MrBeeboh/JeNo7-Sentinel-RTK/JeNo-7-main/04-TPU-HISTORY/JeNo7_1.0.0_Session_High_Tilt.stl

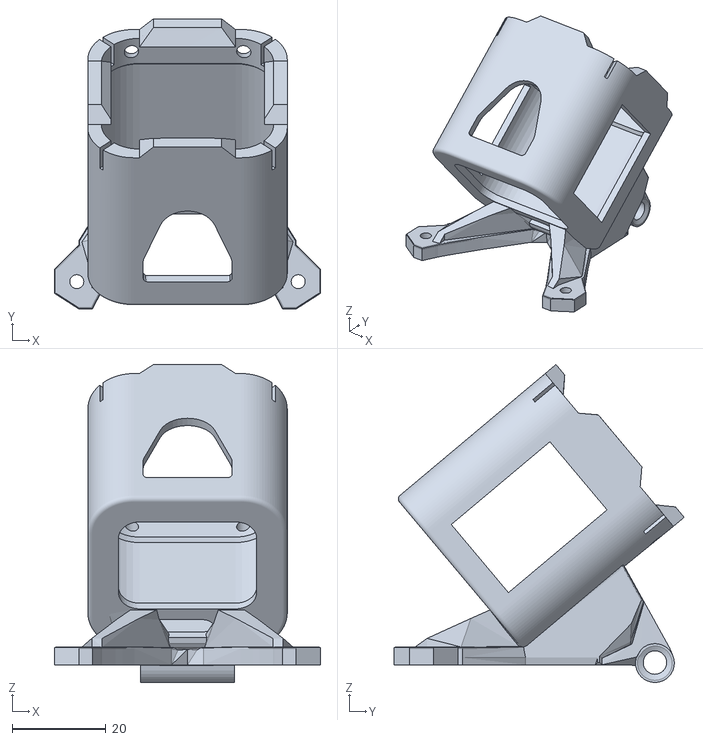
[picture p15: CAD file, 2026-07-24]
JeNo-7-main/04-TPU-HISTORY/JeNo7_1.0.0_Session_High_Tilt.stl
56.9 x 62.0 x 67.9
