MrBeeboh/JeNo7-Sentinel-RTK/Sentinel-on-JeNo7/LR900_Mount.stl

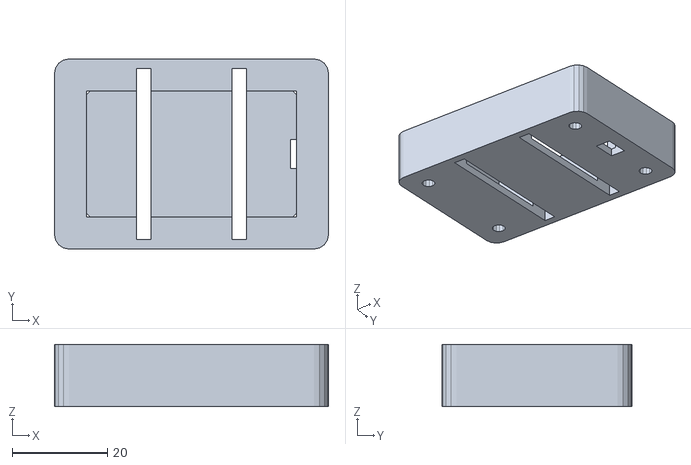
[picture p16: CAD file, 2026-07-24]
Sentinel-on-JeNo7/LR900_Mount.stl
57.4 x 39.8 x 13.0
