MrBeeboh/JeNo7-Sentinel-RTK/Editable/01-CARBON-3D/Arm_key_EditReady.FCStd

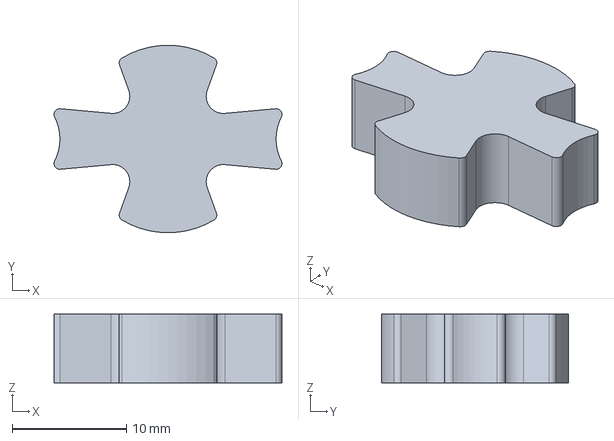
[picture p17: CAD file, 2026-07-24]
Editable/01-CARBON-3D/Arm_key_EditReady.FCStd
20.0 x 16.4 x 6.00 mm
