MrBeeboh/JeNo7-Sentinel-RTK/Editable/02-CARBON-2D-DXF/from-step-projection/Middle_plate_2p5mm.dxf

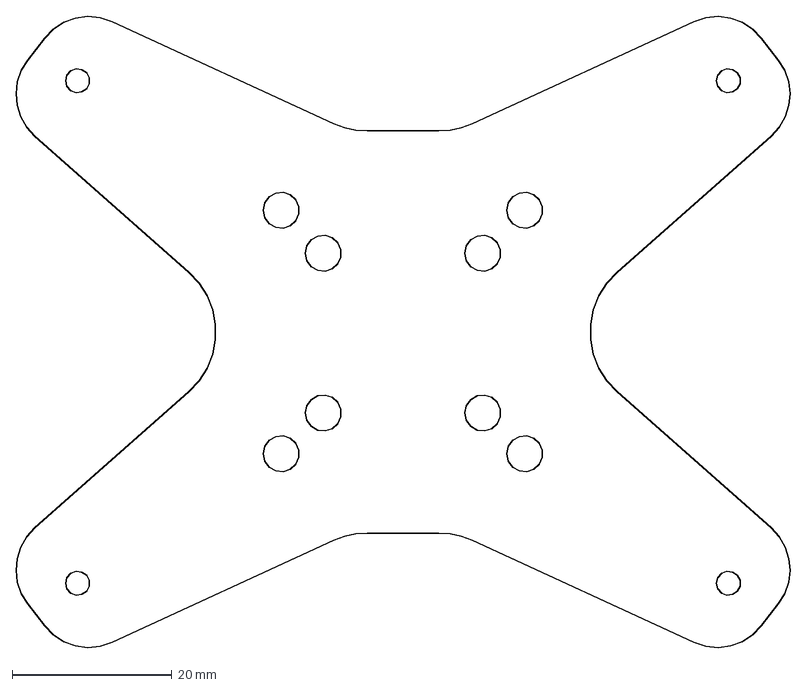
[picture p19: CAD file, 2026-07-24]
Editable/02-CARBON-2D-DXF/from-step-projection/Middle_plate_2p5mm.dxf
96.9 x 79.0 mm
