MrBeeboh/JeNo7-Sentinel-RTK/Editable/03-TPU-3D/from-assembly-STEP/TPU_Rear_bumper.step

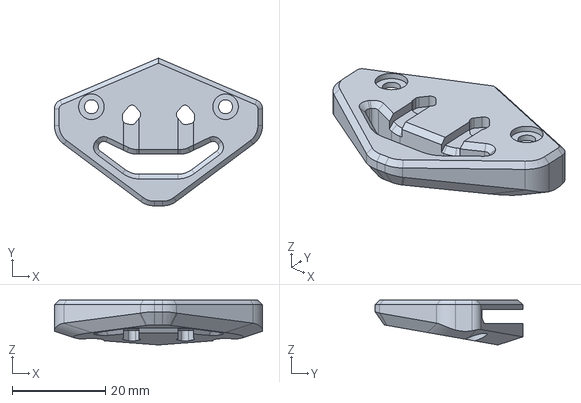
[picture p20: CAD file, 2026-07-24]
Editable/03-TPU-3D/from-assembly-STEP/TPU_Rear_bumper.step
44.7 x 31.8 x 9.65 mm
