MrBeeboh/JeNo7-Sentinel-RTK/JeNo-7-main/02-TPU/JeNo7_Antenna_Double_SMA.stl

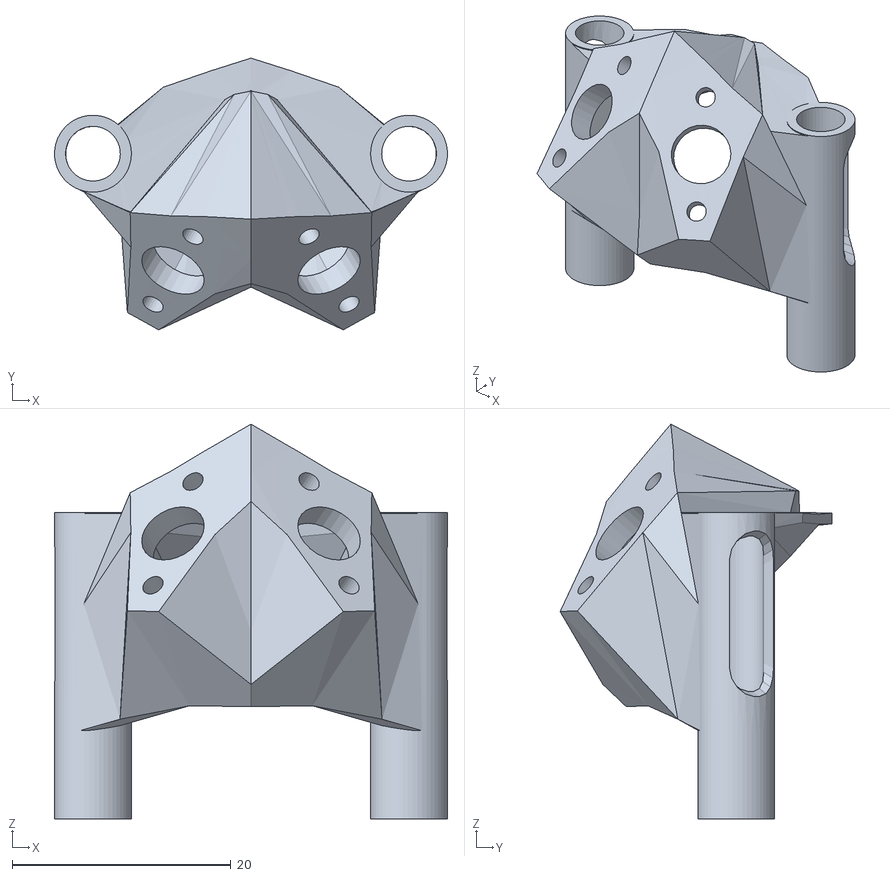
[picture p21: CAD file, 2026-07-24]
JeNo-7-main/02-TPU/JeNo7_Antenna_Double_SMA.stl
35.9 x 24.8 x 36.1
