MrBeeboh/JeNo7-Sentinel-RTK/JeNo-7-main/04-TPU-HISTORY/JeNo7_1.0.0_Soft_Mount_Cine_Plate.stl

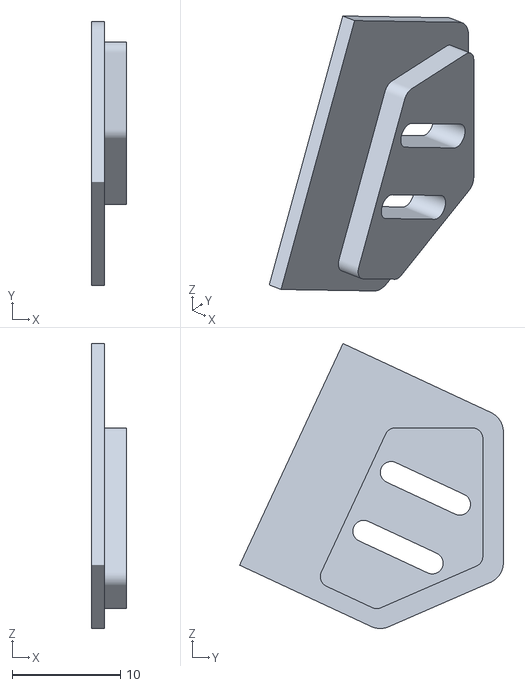
[picture p22: CAD file, 2026-07-24]
JeNo-7-main/04-TPU-HISTORY/JeNo7_1.0.0_Soft_Mount_Cine_Plate.stl
3.20 x 24.4 x 26.4
