MrBeeboh/JeNo7-Sentinel-RTK/Sentinel-on-JeNo7/RP3_Mount.stl

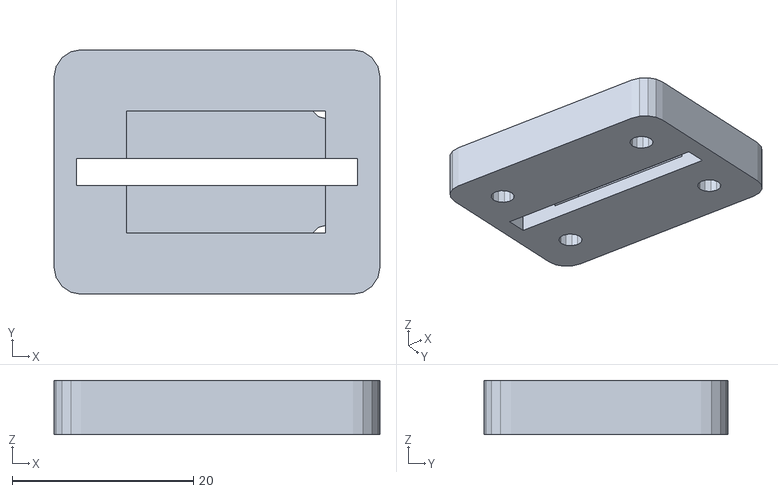
[picture p23: CAD file, 2026-07-24]
Sentinel-on-JeNo7/RP3_Mount.stl
36.0 x 27.0 x 6.00
