MrBeeboh/JeNo7-Sentinel-RTK/Editable/01-CARBON-3D/Camera_plate_25deg_O4.step

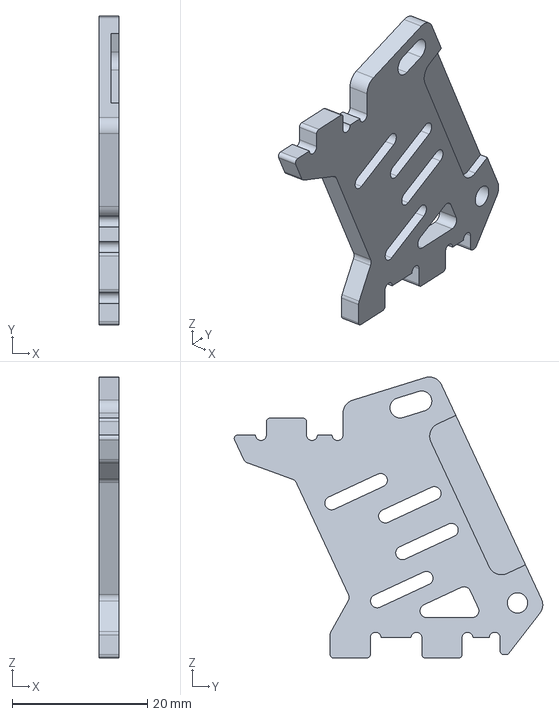
[picture p24: CAD file, 2026-07-24]
Editable/01-CARBON-3D/Camera_plate_25deg_O4.step
3.00 x 45.7 x 41.6 mm
