MrBeeboh/JeNo7-Sentinel-RTK/Editable/02-CARBON-2D-DXF/from-step-projection/Top_plate_2p5mm.dxf

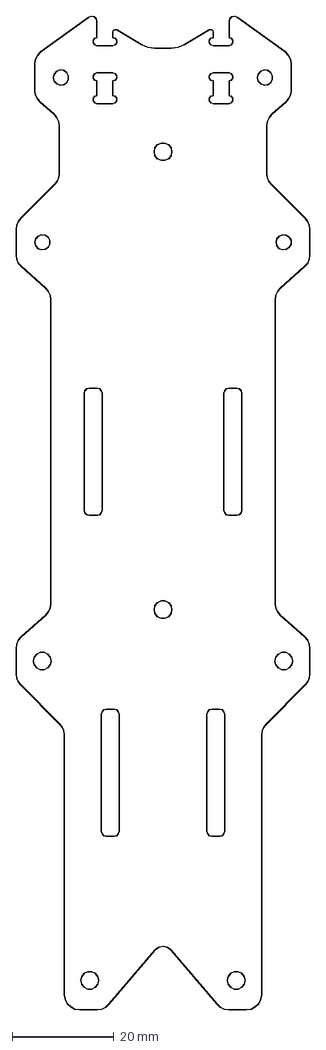
[picture p26: CAD file, 2026-07-24]
Editable/02-CARBON-2D-DXF/from-step-projection/Top_plate_2p5mm.dxf
57.8 x 195.4 mm
