MrBeeboh/JeNo7-Sentinel-RTK/Editable/03-TPU-3D/from-assembly-STEP/TPU_Antenna_support.step

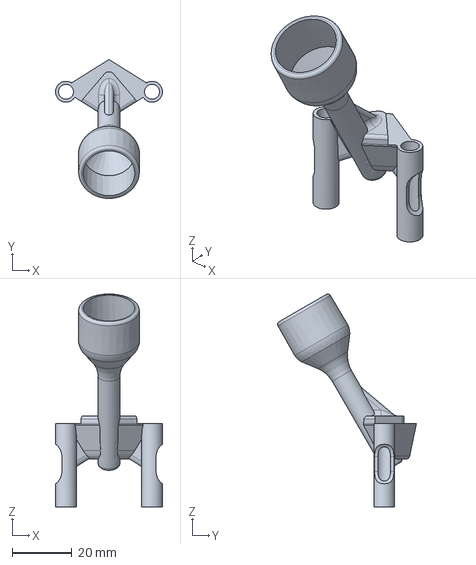
[picture p27: CAD file, 2026-07-24]
Editable/03-TPU-3D/from-assembly-STEP/TPU_Antenna_support.step
35.8 x 46.5 x 71.3 mm
