MrBeeboh/JeNo7-Sentinel-RTK/JeNo-7-main/04-TPU-HISTORY/JeNo7_1.0.0_Gopro_40deg.stl

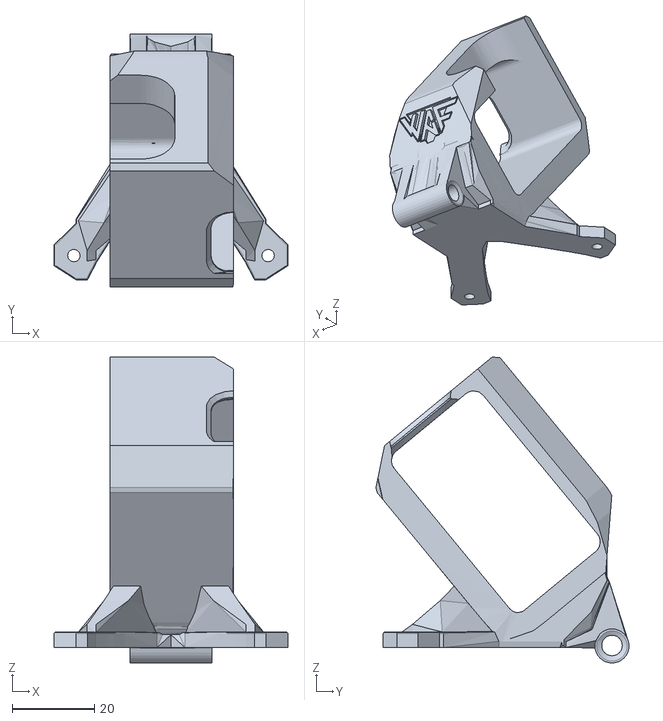
[picture p28: CAD file, 2026-07-24]
JeNo-7-main/04-TPU-HISTORY/JeNo7_1.0.0_Gopro_40deg.stl
56.9 x 61.6 x 74.5
