MrBeeboh/JeNo7-Sentinel-RTK/Sentinel-on-JeNo7/GNSS_Roof_Plate.stl

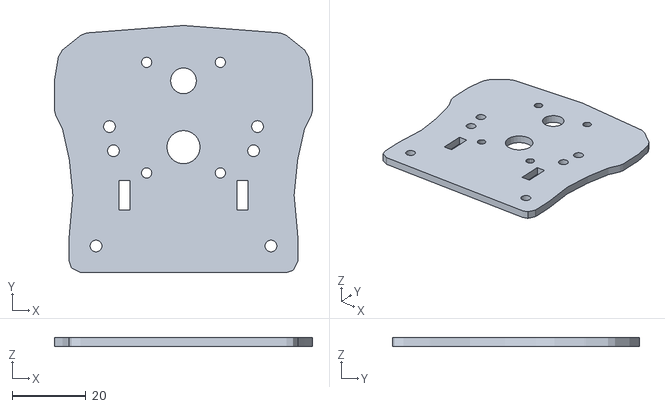
[picture p29: CAD file, 2026-07-24]
Sentinel-on-JeNo7/GNSS_Roof_Plate.stl
70.0 x 67.0 x 2.50
