MrBeeboh/JeNo7-Sentinel-RTK/Editable/01-CARBON-3D/Bottom_plate_3mm_EditReady.FCStd

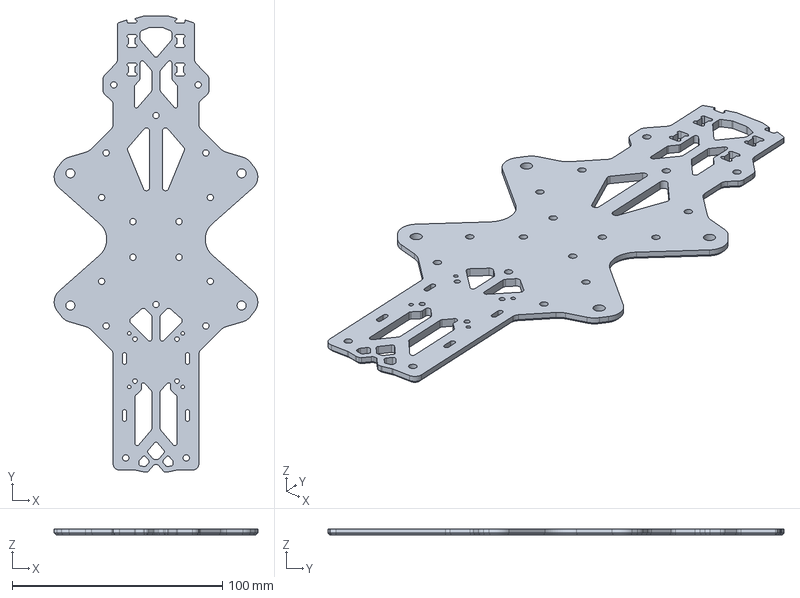
[picture p30: CAD file, 2026-07-24]
Editable/01-CARBON-3D/Bottom_plate_3mm_EditReady.FCStd
96.9 x 217.1 x 3.00 mm
