MrBeeboh/JeNo7-Sentinel-RTK/Editable/02-CARBON-2D-DXF/from-all-versions-dxf/Arm_or_reinforcement_14.dxf

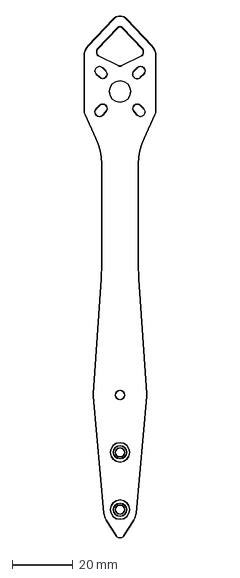
[picture p31: CAD file, 2026-07-24]
Editable/02-CARBON-2D-DXF/from-all-versions-dxf/Arm_or_reinforcement_14.dxf
23.5 x 171.2 mm
