MrBeeboh/JeNo7-Sentinel-RTK/Editable/02-CARBON-2D-DXF/from-step-projection/Arm_key.dxf

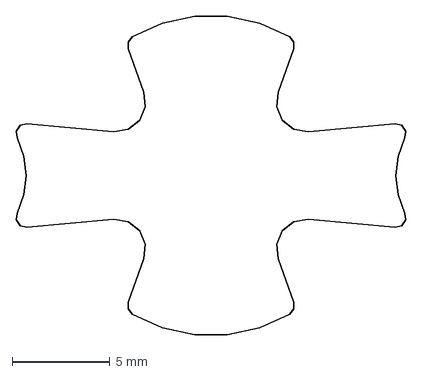
[picture p32: CAD file, 2026-07-24]
Editable/02-CARBON-2D-DXF/from-step-projection/Arm_key.dxf
19.9 x 16.3 mm
