MrBeeboh/JeNo7-Sentinel-RTK/JeNo-7-main/02-TPU/JeNo7_Antenna_Front_RX_Support.stl

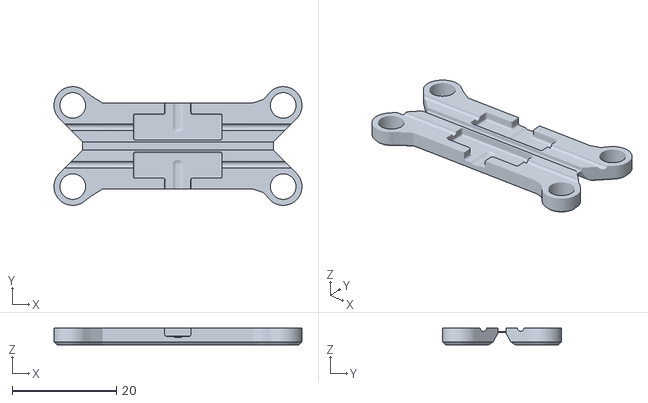
[picture p33: CAD file, 2026-07-24]
JeNo-7-main/02-TPU/JeNo7_Antenna_Front_RX_Support.stl
47.5 x 22.7 x 3.20
