MrBeeboh/JeNo7-Sentinel-RTK/JeNo-7-main/04-TPU-HISTORY/JeNo7_1.0.0_Gopro_25deg.stl

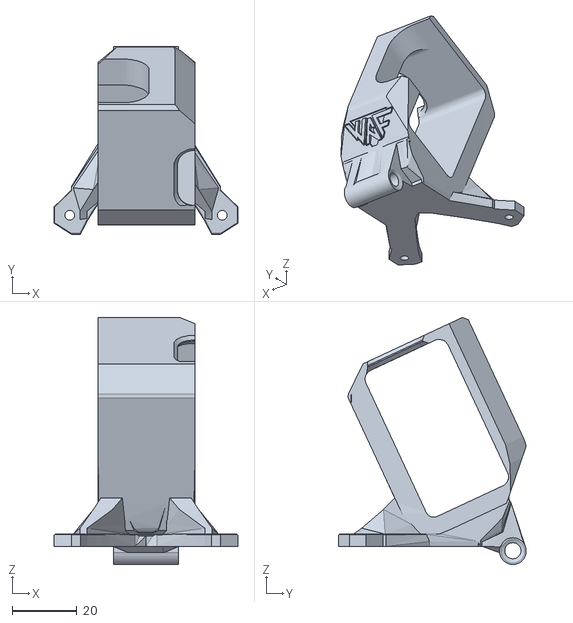
[picture p34: CAD file, 2026-07-24]
JeNo-7-main/04-TPU-HISTORY/JeNo7_1.0.0_Gopro_25deg.stl
56.9 x 58.1 x 76.5
