MrBeeboh/JeNo7-Sentinel-RTK/Sentinel-on-JeNo7/GNSS_Roof_Plate_fc.step

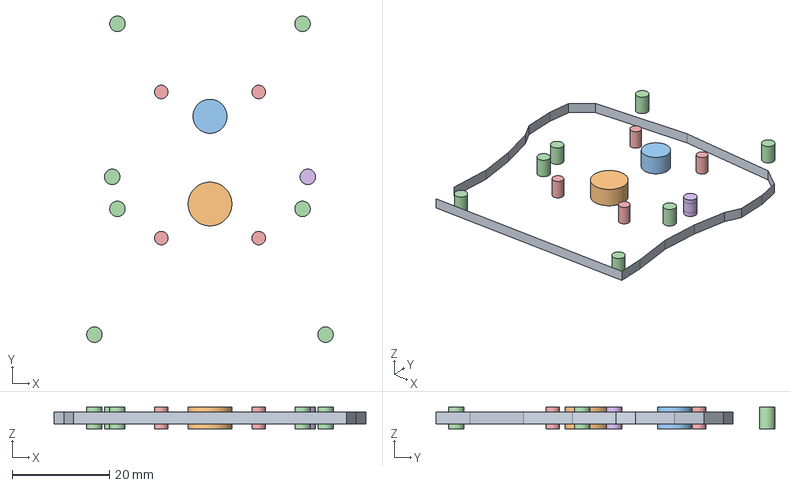
[picture p35: CAD file, 2026-07-24]
Sentinel-on-JeNo7/GNSS_Roof_Plate_fc.step
64.0 x 69.6 x 4.50 mm
