MrBeeboh/JeNo7-Sentinel-RTK/Editable/02-CARBON-2D-DXF/from-all-versions-dxf/Plate_22_20x16mm.dxf

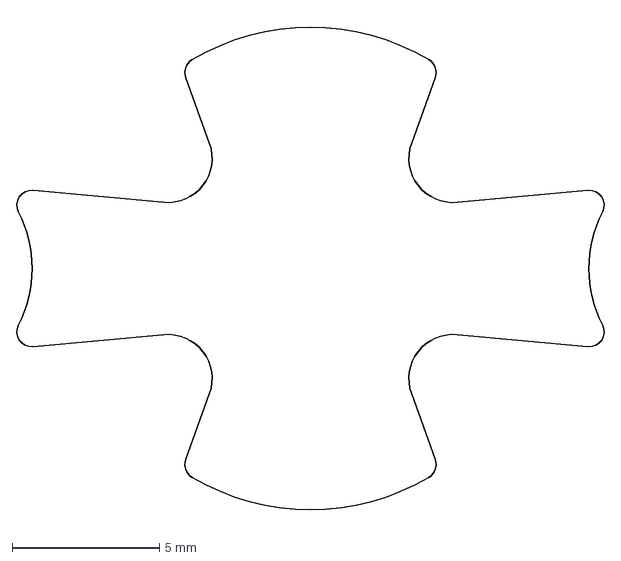
[picture p36: CAD file, 2026-07-24]
Editable/02-CARBON-2D-DXF/from-all-versions-dxf/Plate_22_20x16mm.dxf
20.0 x 17.1 mm
