MrBeeboh/JeNo7-Sentinel-RTK/Editable/02-CARBON-2D-DXF/from-step-projection/Bottom_plate_3mm.dxf

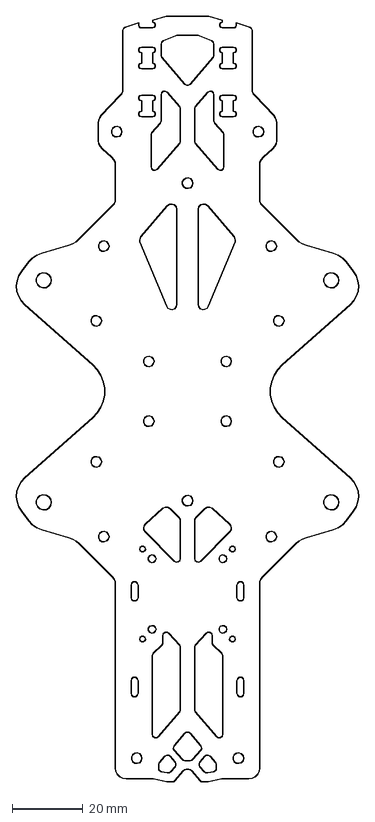
[picture p37: CAD file, 2026-07-24]
Editable/02-CARBON-2D-DXF/from-step-projection/Bottom_plate_3mm.dxf
96.9 x 217.1 mm
