MrBeeboh/JeNo7-Sentinel-RTK/JeNo-7-main/02-TPU/JeNo7_Arm_6mm.stl

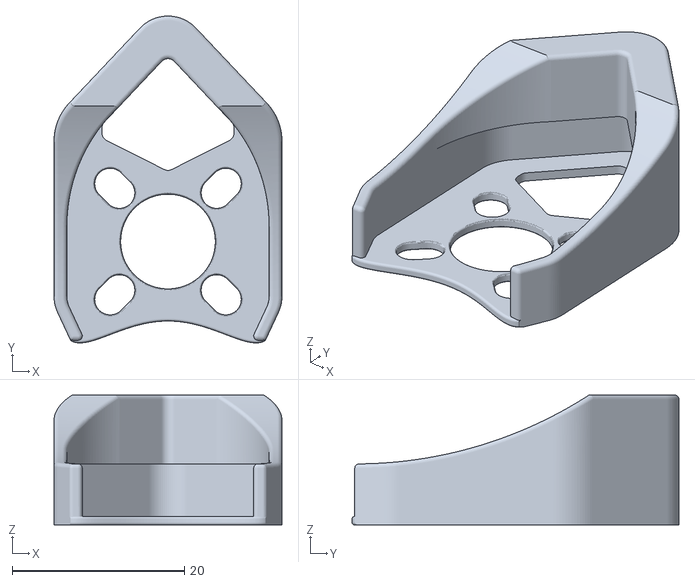
[picture p38: CAD file, 2026-07-24]
JeNo-7-main/02-TPU/JeNo7_Arm_6mm.stl
26.5 x 38.0 x 15.1
