MrBeeboh/JeNo7-Sentinel-RTK/Editable/01-CARBON-3D/Arm_8mm.step

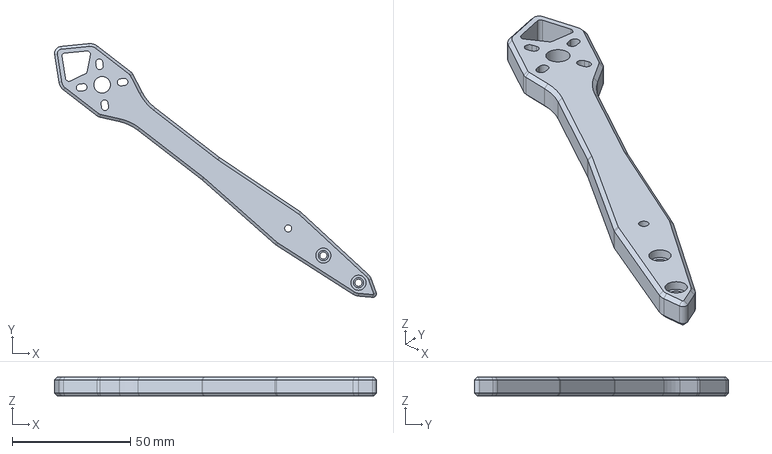
[picture p39: CAD file, 2026-07-24]
Editable/01-CARBON-3D/Arm_8mm.step
136.4 x 107.6 x 8.00 mm
