MrBeeboh/JeNo7-Sentinel-RTK/JeNo-7-main/02-TPU/JeNo7_Soft_Mount_Cine_Plate_O3_O4.stl

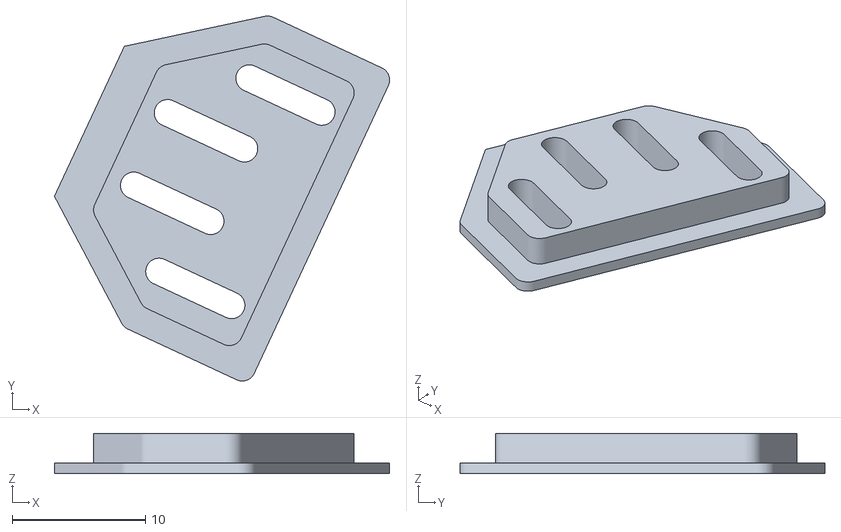
[picture p40: CAD file, 2026-07-24]
JeNo-7-main/02-TPU/JeNo7_Soft_Mount_Cine_Plate_O3_O4.stl
25.1 x 27.4 x 3.00
