MrBeeboh/JeNo7-Sentinel-RTK/Editable/02-CARBON-2D-DXF/from-all-versions-dxf/Top_plate_variant_05.dxf

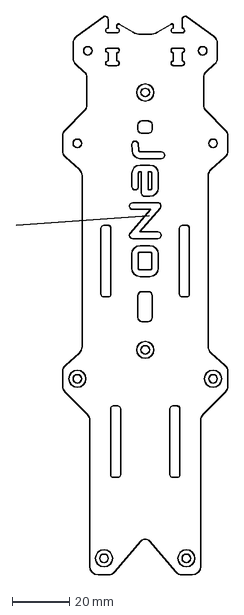
[picture p41: CAD file, 2026-07-24]
Editable/02-CARBON-2D-DXF/from-all-versions-dxf/Top_plate_variant_05.dxf
74.0 x 195.5 mm
