MrBeeboh/JeNo7-Sentinel-RTK/Editable/02-CARBON-2D-DXF/from-all-versions-dxf/Camera_plate_variant_09.dxf

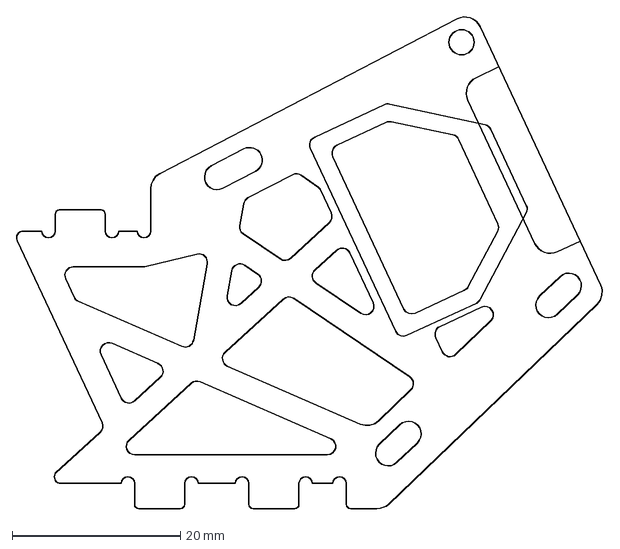
[picture p42: CAD file, 2026-07-24]
Editable/02-CARBON-2D-DXF/from-all-versions-dxf/Camera_plate_variant_09.dxf
69.8 x 58.5 mm
