MrBeeboh/JeNo7-Sentinel-RTK/JeNo-7-main/02-TPU/JeNo7_Capacitor_50V_Spike_Support.stl

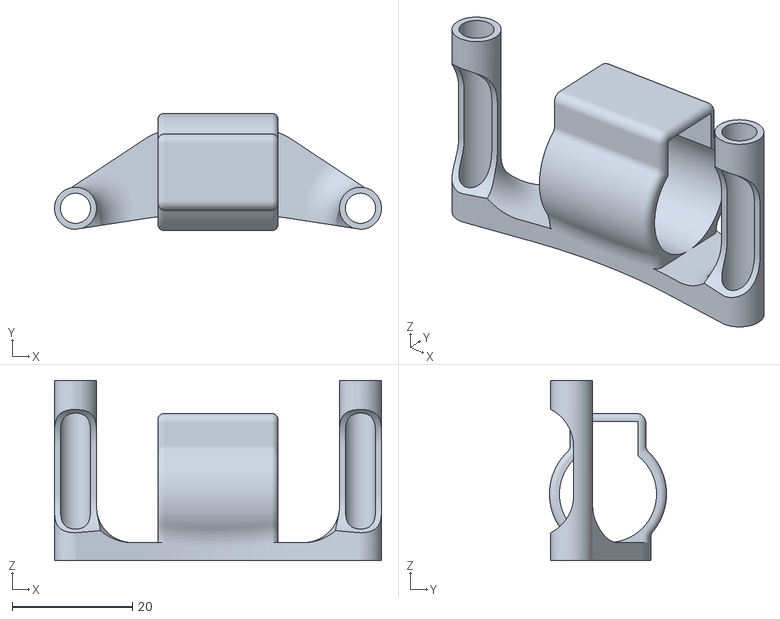
[picture p43: CAD file, 2026-07-24]
JeNo-7-main/02-TPU/JeNo7_Capacitor_50V_Spike_Support.stl
54.5 x 19.5 x 30.0
