MrBeeboh/JeNo7-Sentinel-RTK/Editable/02-CARBON-2D-DXF/from-all-versions-dxf/Plate_20_46x42mm.dxf

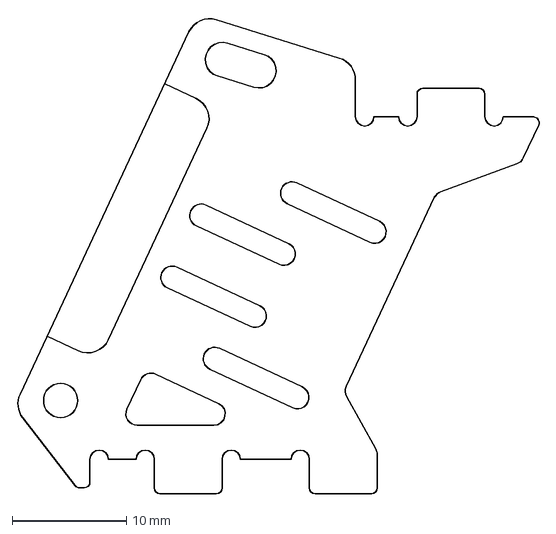
[picture p44: CAD file, 2026-07-24]
Editable/02-CARBON-2D-DXF/from-all-versions-dxf/Plate_20_46x42mm.dxf
45.8 x 41.8 mm
