MrBeeboh/JeNo7-Sentinel-RTK/Editable/02-CARBON-2D-DXF/from-all-versions-dxf/Arm_or_reinforcement_08.dxf

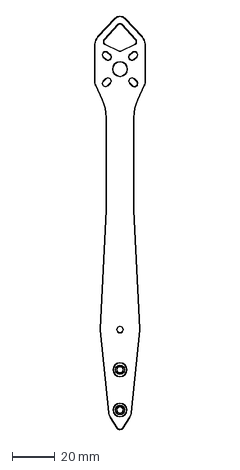
[picture p46: CAD file, 2026-07-24]
Editable/02-CARBON-2D-DXF/from-all-versions-dxf/Arm_or_reinforcement_08.dxf
23.5 x 193.7 mm
