MrBeeboh/JeNo7-Sentinel-RTK/JeNo-7-main/02-TPU/JeNo7_Antenna_SMA_T-Antenna.stl

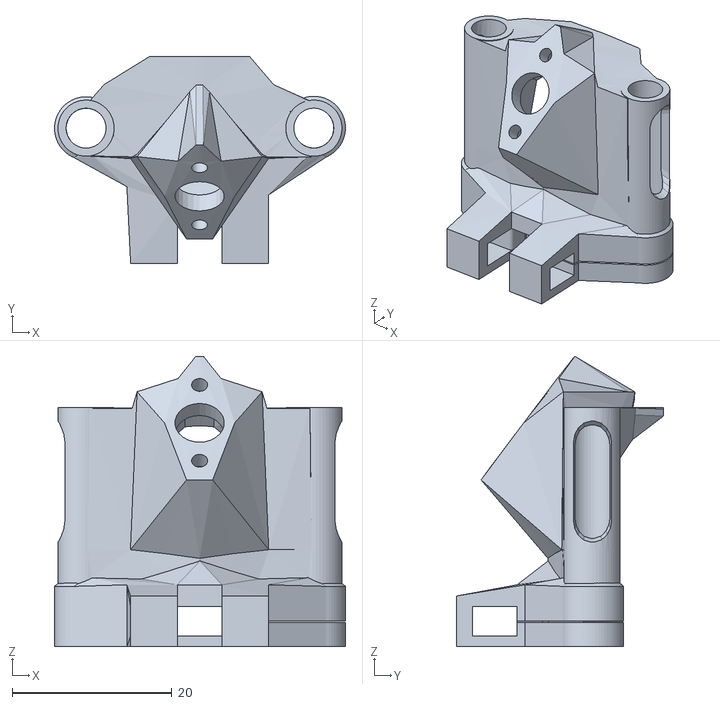
[picture p47: CAD file, 2026-07-24]
JeNo-7-main/02-TPU/JeNo7_Antenna_SMA_T-Antenna.stl
36.4 x 25.9 x 36.4
