MrBeeboh/JeNo7-Sentinel-RTK/Editable/02-CARBON-2D-DXF/from-all-versions-dxf/Middle_plate_variant_07.dxf

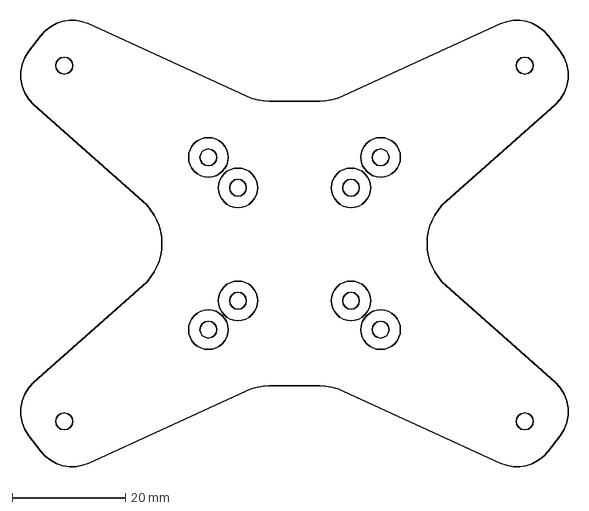
[picture p48: CAD file, 2026-07-24]
Editable/02-CARBON-2D-DXF/from-all-versions-dxf/Middle_plate_variant_07.dxf
98.5 x 80.5 mm
