MrBeeboh/JeNo7-Sentinel-RTK/Editable/02-CARBON-2D-DXF/from-all-versions-dxf/Plate_18_52x43mm.dxf

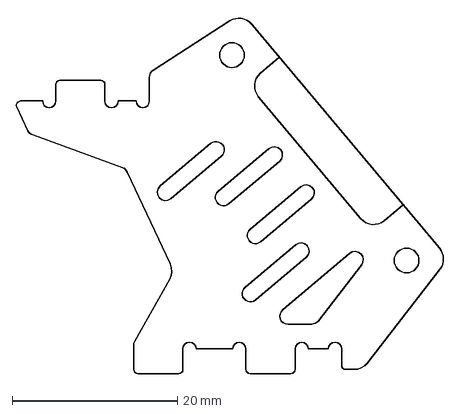
[picture p50: CAD file, 2026-07-24]
Editable/02-CARBON-2D-DXF/from-all-versions-dxf/Plate_18_52x43mm.dxf
51.9 x 43.2 mm
