MrBeeboh/JeNo7-Sentinel-RTK/Editable/02-CARBON-2D-DXF/from-all-versions-dxf/Bottom_plate_variant_02.dxf

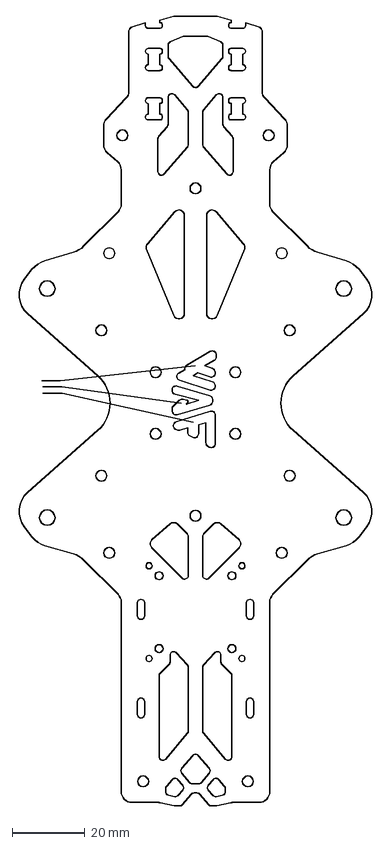
[picture p52: CAD file, 2026-07-24]
Editable/02-CARBON-2D-DXF/from-all-versions-dxf/Bottom_plate_variant_02.dxf
98.5 x 217.1 mm
