MrBeeboh/JeNo7-Sentinel-RTK/Editable/02-CARBON-2D-DXF/from-all-versions-dxf/Camera_plate_variant_10.dxf

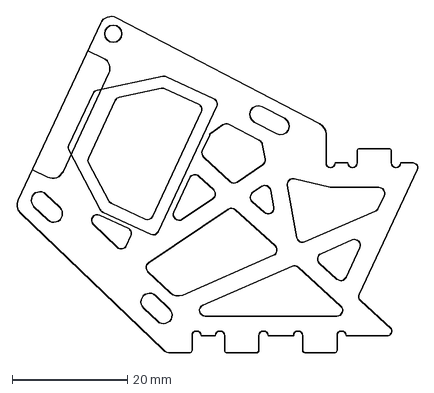
[picture p54: CAD file, 2026-07-24]
Editable/02-CARBON-2D-DXF/from-all-versions-dxf/Camera_plate_variant_10.dxf
69.8 x 58.5 mm
