MrBeeboh/JeNo7-Sentinel-RTK/Editable/02-CARBON-2D-DXF/from-all-versions-dxf/Top_plate_variant_03.dxf

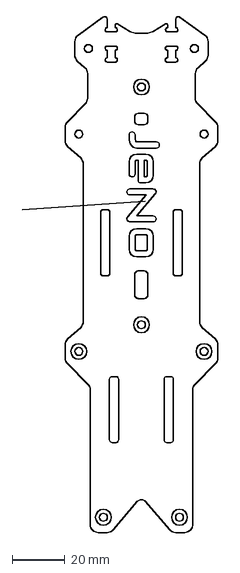
[picture p55: CAD file, 2026-07-24]
Editable/02-CARBON-2D-DXF/from-all-versions-dxf/Top_plate_variant_03.dxf
74.0 x 195.5 mm
