MrBeeboh/JeNo7-Sentinel-RTK/Editable/02-CARBON-2D-DXF/from-all-versions-dxf/Arm_or_reinforcement_17.dxf

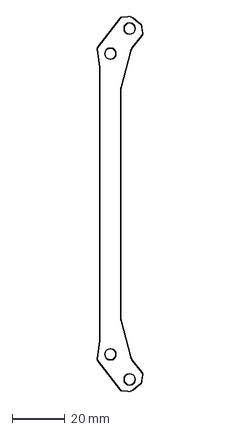
[picture p56: CAD file, 2026-07-24]
Editable/02-CARBON-2D-DXF/from-all-versions-dxf/Arm_or_reinforcement_17.dxf
17.2 x 141.9 mm
