MrBeeboh/JeNo7-Sentinel-RTK/Editable/02-CARBON-2D-DXF/from-all-versions-dxf/Camera_plate_variant_15.dxf

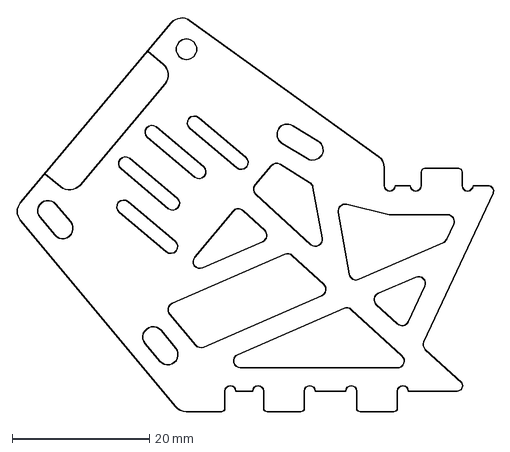
[picture p57: CAD file, 2026-07-24]
Editable/02-CARBON-2D-DXF/from-all-versions-dxf/Camera_plate_variant_15.dxf
69.7 x 57.7 mm
