MrBeeboh/JeNo7-Sentinel-RTK/Editable/02-CARBON-2D-DXF/from-all-versions-dxf/Top_plate_variant_04.dxf

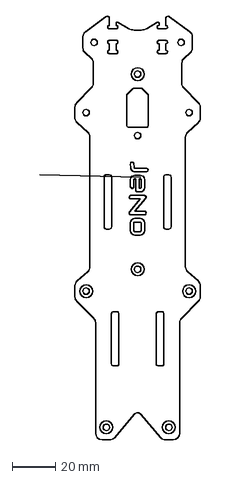
[picture p59: CAD file, 2026-07-24]
Editable/02-CARBON-2D-DXF/from-all-versions-dxf/Top_plate_variant_04.dxf
74.0 x 195.5 mm
